Team-robOTTO/PowerBoard/software/teensy/arduino/powerboard/globals.h

/*
 * robOTTOs powerboard teensy firmware
 * global definitions (globals.h)
 * created: 16/MAY/2021 
 */

#define PIN_LED_BAT1_GREEN 20
#define PIN_LED_BAT1_RED 21
#define PIN_LED_BAT2_GREEN 18
#define PIN_LED_BAT2_RED 19
#define PIN_LED_EXT_RED 17
#define PIN_LED_EXT_GREEN 16

#define BAT_EMPTY 17500.0f // V
#define PS_PLUGGED_IN 22000.0f // V

#define PIN_HIGH_SIDE_BASE 14
#define PIN_HIGH_SIDE_ARM 15
